MintyTrebor/MK2s-SKR-1.4-TFT35-2209-RRF-Hemera/MK3s_Hemera_Adapter_V3_plate.stl

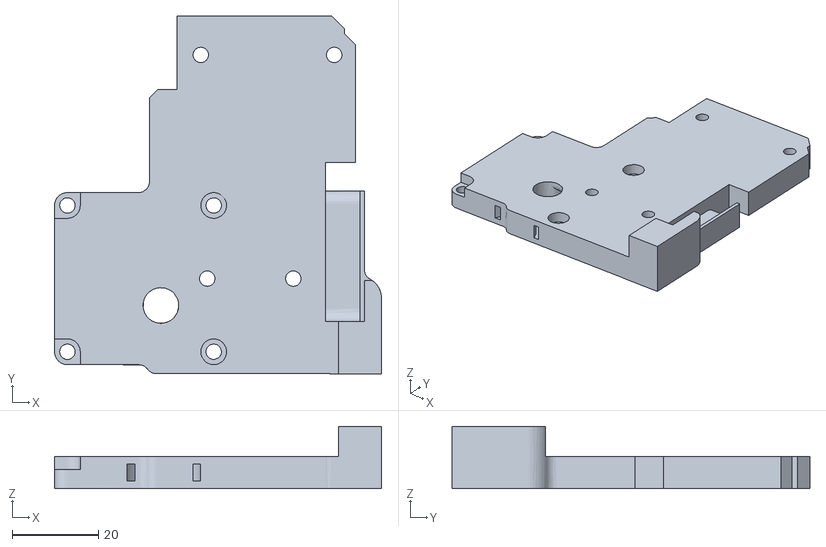
[picture p15: CAD file, 2020-08-26]
MK3s_Hemera_Adapter_V3_plate.stl
76.0 x 83.2 x 14.5
