MintyTrebor/MK2s-SKR-1.4-TFT35-2209-RRF-Hemera/x-carriage-back.stl

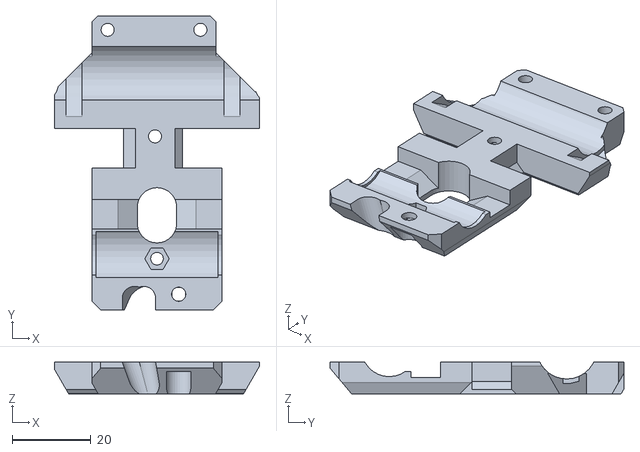
[picture p16: CAD file, 2020-08-26]
x-carriage-back.stl
52.0 x 74.5 x 8.00
