MintyTrebor/MK2s-SKR-1.4-TFT35-2209-RRF-Hemera/Camera Plate.stl

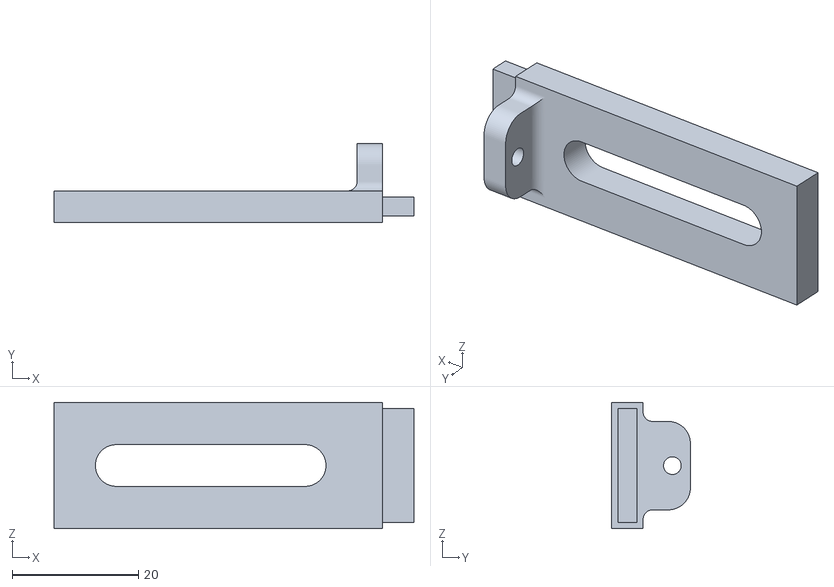
[picture p17: CAD file, 2020-08-26]
Camera Plate.stl
57.0 x 12.5 x 20.0
