MintyTrebor/MK2s-SKR-1.4-TFT35-2209-RRF-Hemera/Z Top Mount Left v2.stl

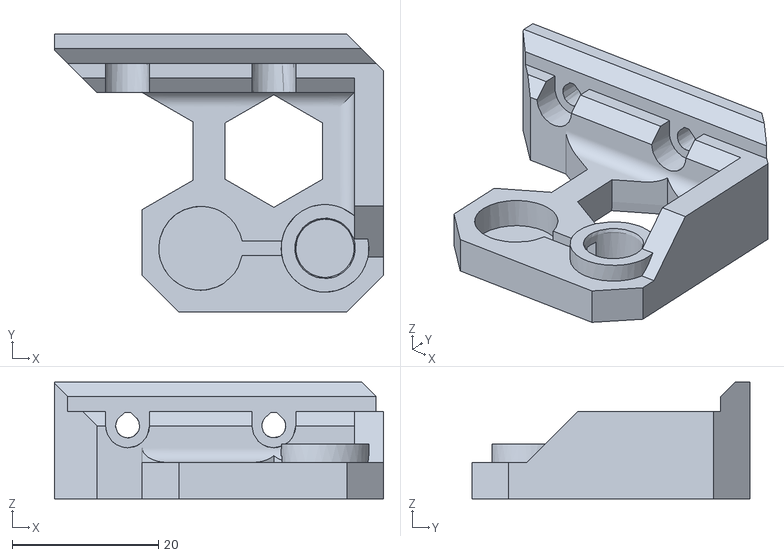
[picture p18: CAD file, 2020-08-26]
Z Top Mount Left v2.stl
45.0 x 38.0 x 16.0
