MintyTrebor/MK2s-SKR-1.4-TFT35-2209-RRF-Hemera/BTT TFT35 Case v1.stl

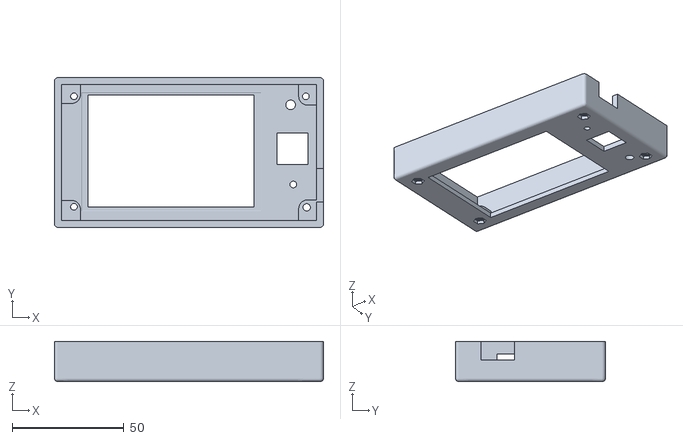
[picture p19: CAD file, 2020-08-26]
BTT TFT35 Case v1.stl
120.3 x 67.0 x 18.0
