MintyTrebor/MK2s-SKR-1.4-TFT35-2209-RRF-Hemera/x-carriage.stl

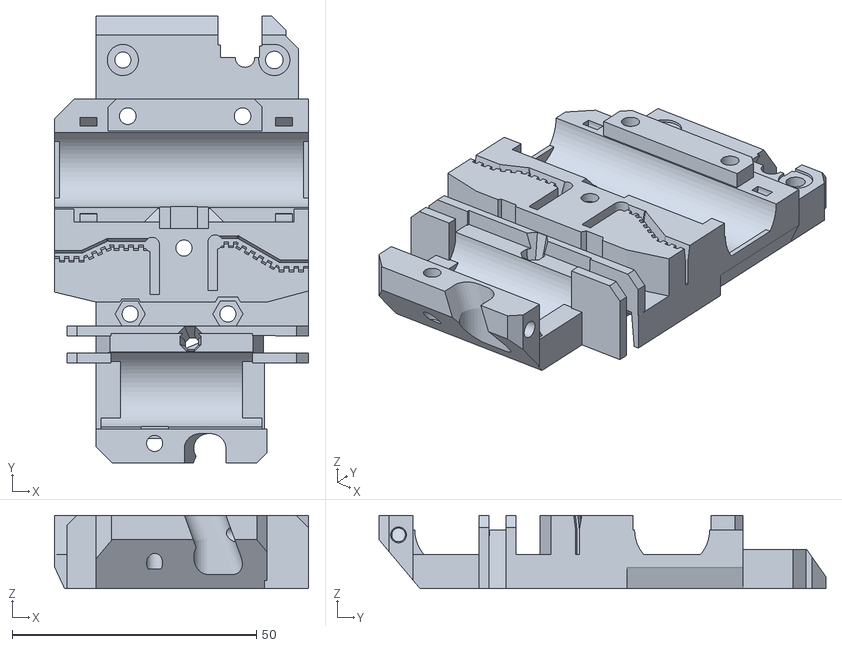
[picture p20: CAD file, 2020-08-26]
x-carriage.stl
52.0 x 91.5 x 15.0
