MintyTrebor/MK2s-SKR-1.4-TFT35-2209-RRF-Hemera/cable-holder.stl

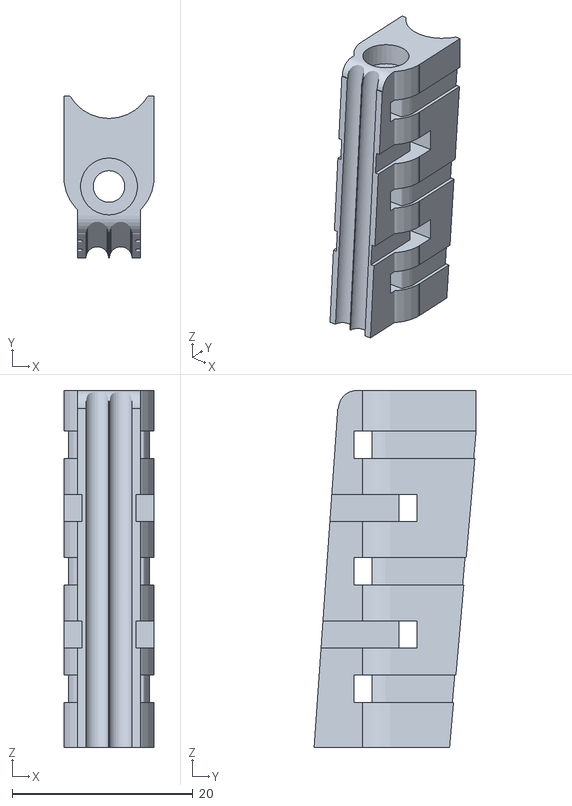
[picture p21: CAD file, 2020-08-26]
cable-holder.stl
10.0 x 17.9 x 39.5
