MintyTrebor/MK2s-SKR-1.4-TFT35-2209-RRF-Hemera/BTT TFT35 LCD Support v1.stl

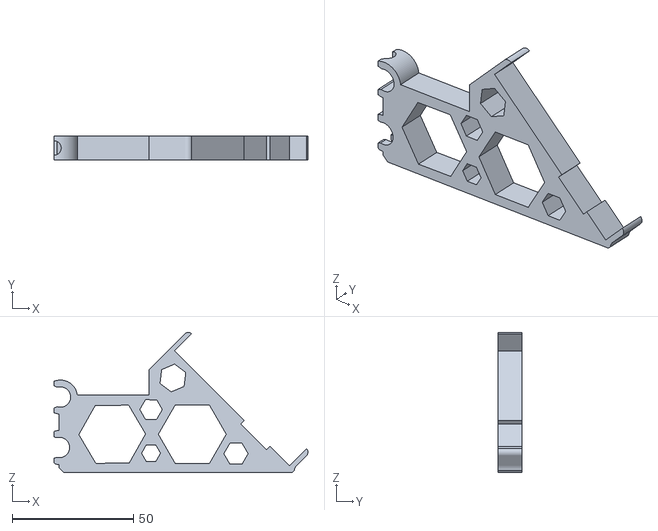
[picture p22: CAD file, 2020-08-26]
BTT TFT35 LCD Support v1.stl
104.7 x 10.00 x 57.8
