MintyTrebor/MK2s-SKR-1.4-TFT35-2209-RRF-Hemera/MK3s_Hemera_Adapter_v2_x_idler (Print +1% xyz in PCarbonate).stl

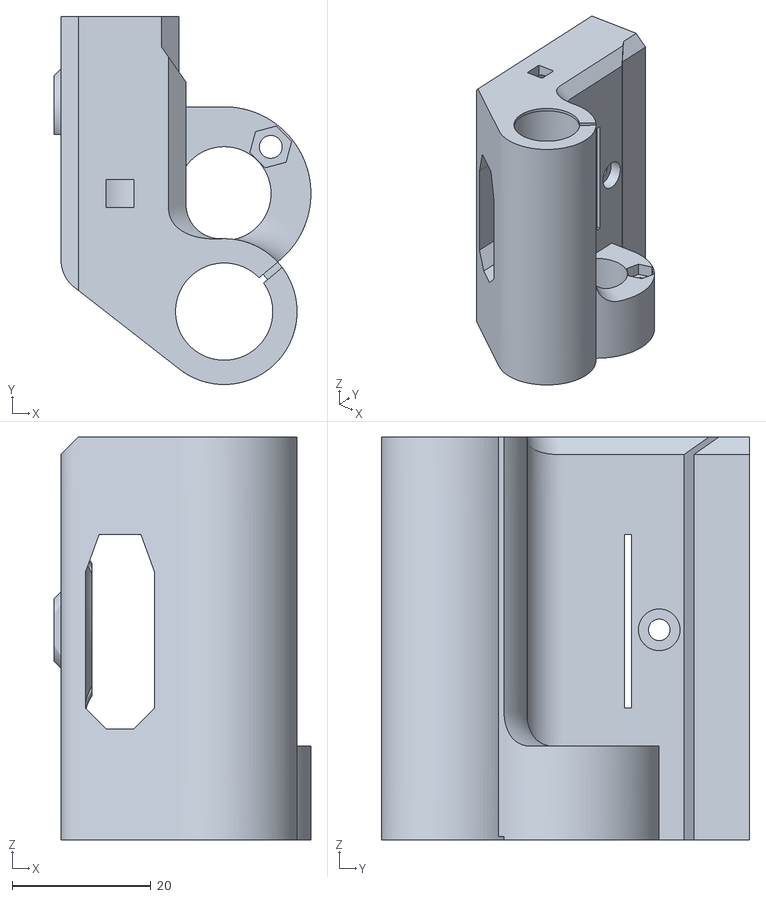
[picture p23: CAD file, 2020-08-26]
MK3s_Hemera_Adapter_v2_x_idler (Print +1% xyz in PCarbonate).stl
37.0 x 53.0 x 58.0
